aabhassenapati/temperature-display-logger/Images/IMG20250813173202.jpg

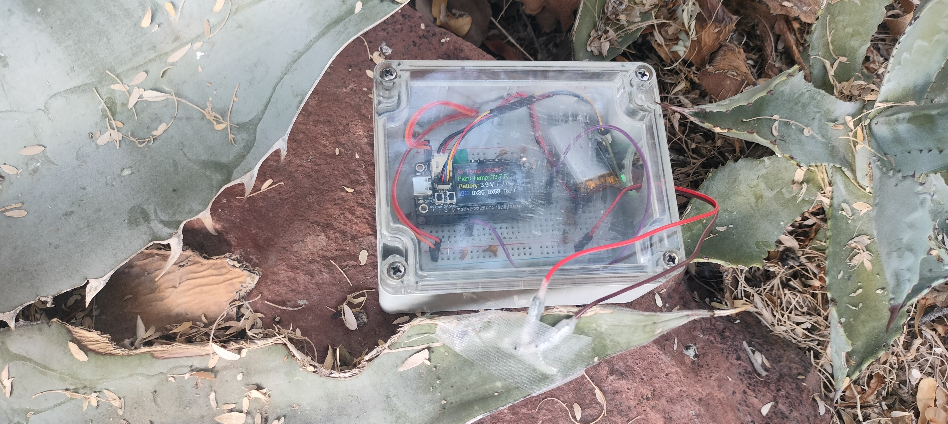
Images/IMG20250813173202.jpg
