aabhassenapati/temperature-display-logger/Images/IMG20250815162052.jpg

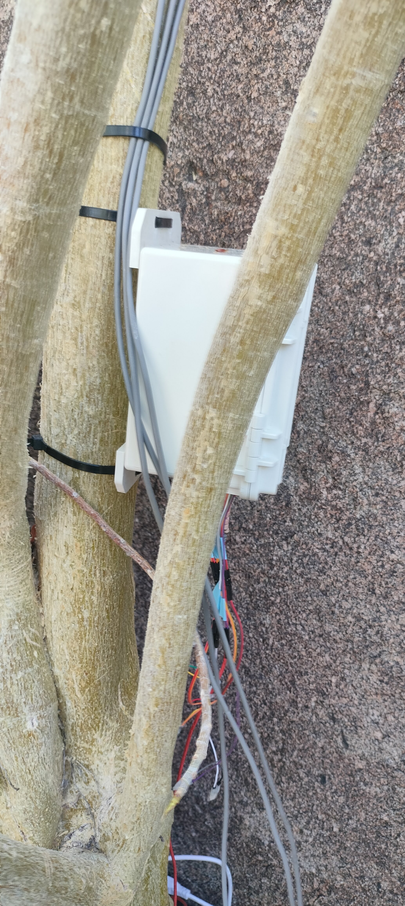
Images/IMG20250815162052.jpg
