aabhassenapati/temperature-display-logger/Images/IMG20250815171557.jpg

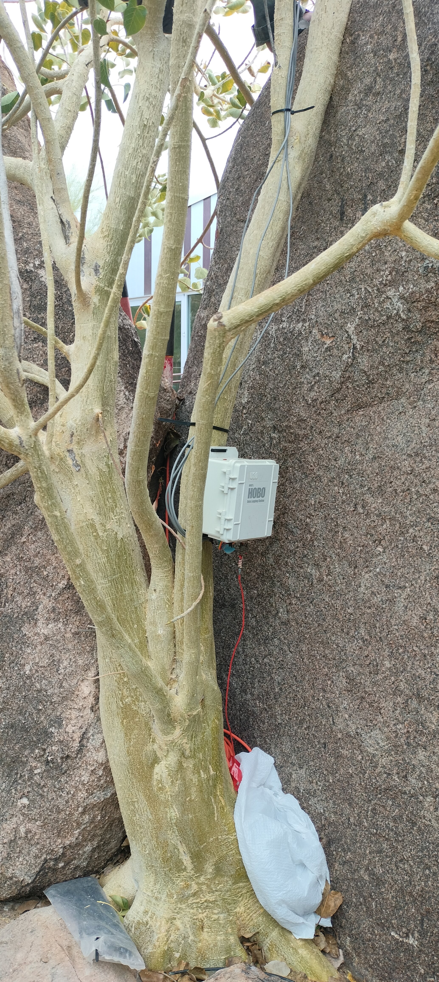
Images/IMG20250815171557.jpg
