aabhassenapati/temperature-display-logger/Images/IMG20250815172234.jpg

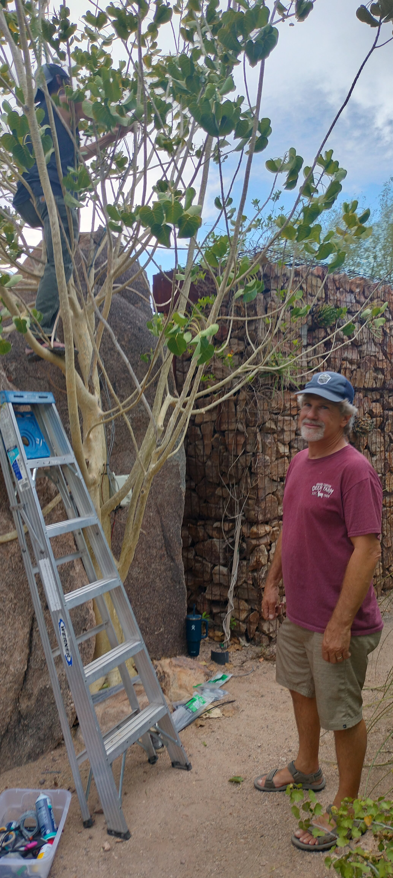
Images/IMG20250815172234.jpg
