aabhassenapati/temperature-display-logger/Images/IMG20250818174235.jpg

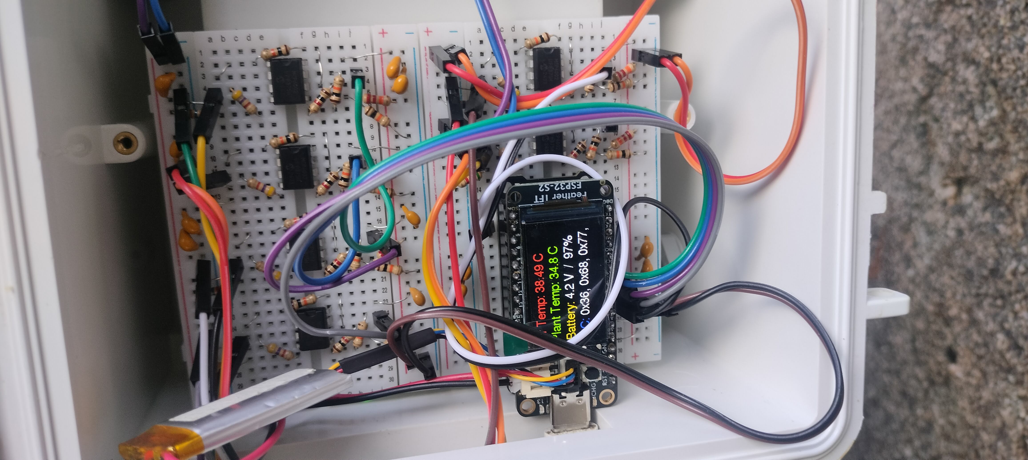
Images/IMG20250818174235.jpg
