aabhassenapati/temperature-display-logger/Images/IMG20250819190731.jpg

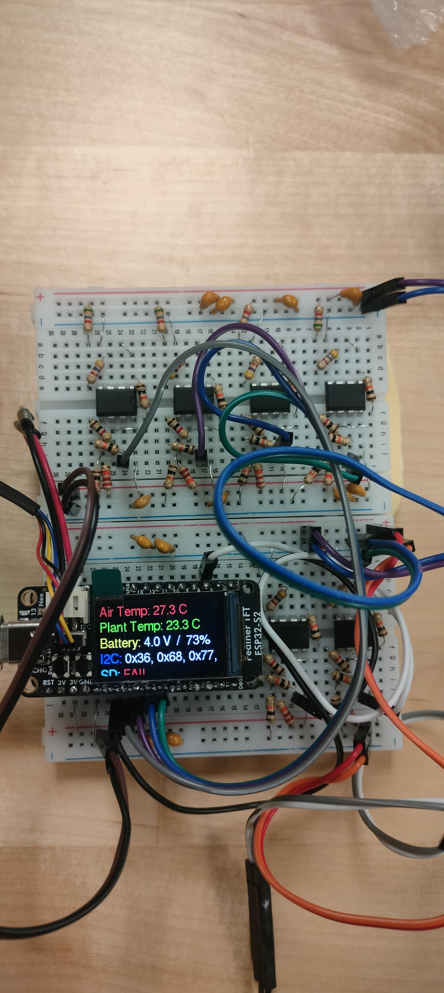
Images/IMG20250819190731.jpg
