aabhassenapati/temperature-display-logger/Images/IMG_2165.jpg

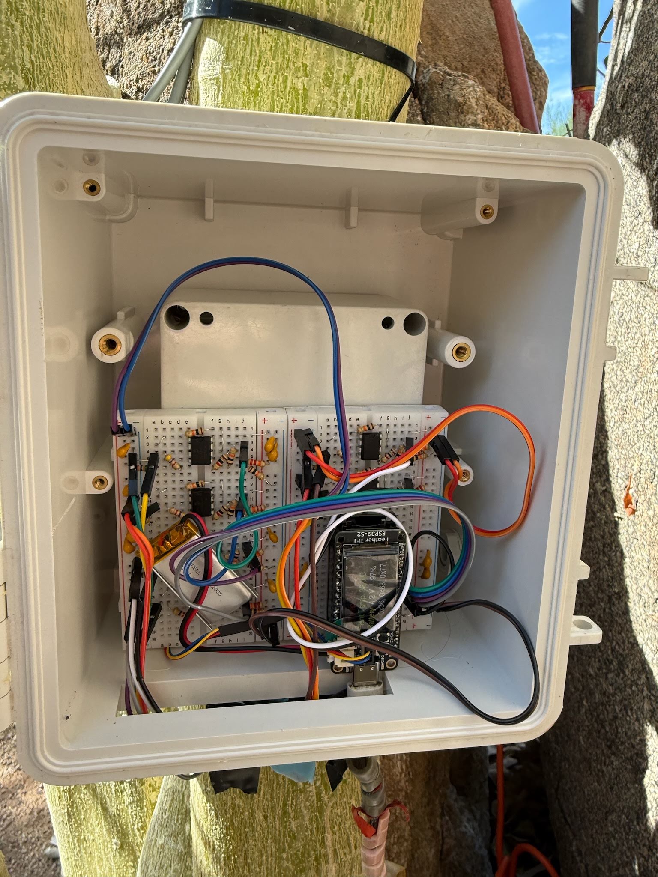
Images/IMG_2165.jpg
