aabhassenapati/temperature-display-logger/Images/IMG_20250822_151914 (4).png

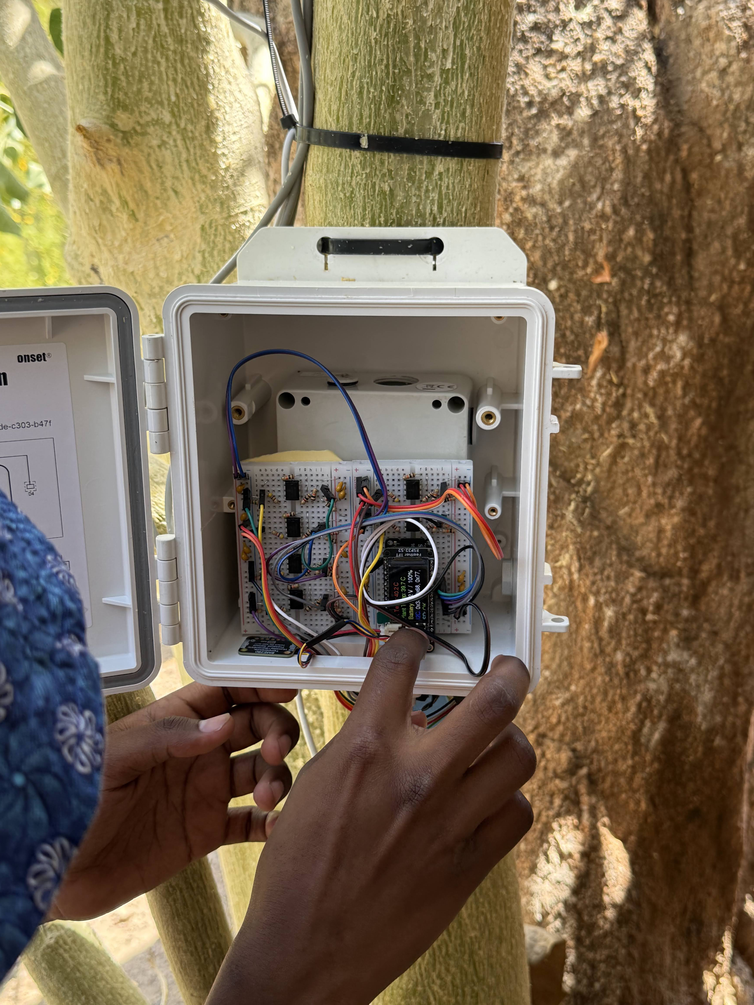
Images/IMG_20250822_151914 (4).png
