aabhassenapati/temperature-display-logger/Images/Screenshot 2025-08-20 at 4.04.33 PM.png

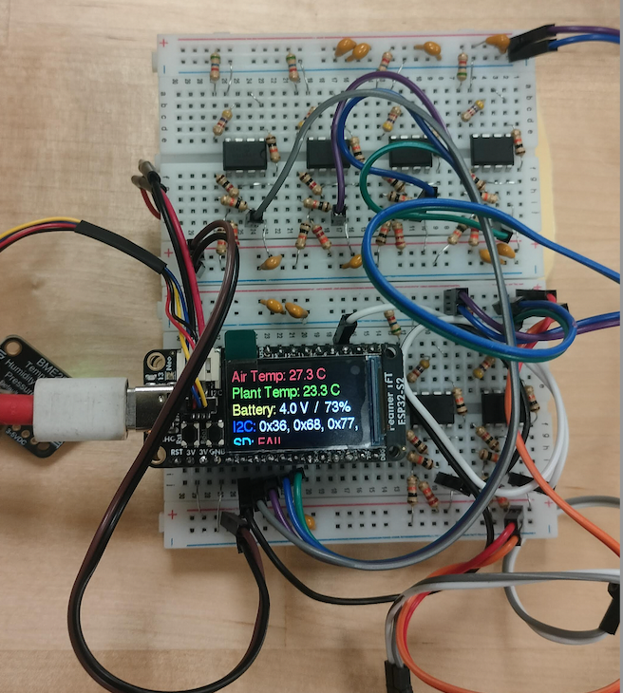
Images/Screenshot 2025-08-20 at 4.04.33 PM.png
