aabhassenapati/temperature-display-logger/Plots/Air Temperature (C) and Relative Humidity (%).png

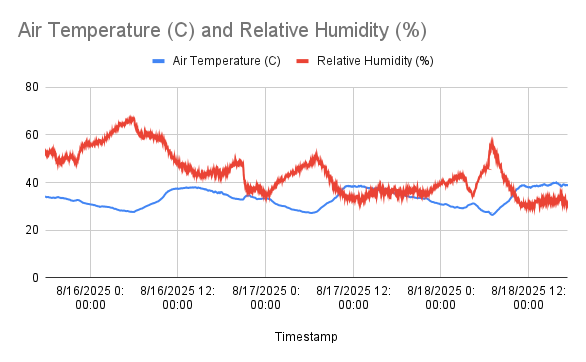
Plots/Air Temperature (C) and Relative Humidity (%).png
