aabhassenapati/temperature-display-logger/Plots/Air Temperature (C) vs Time.png

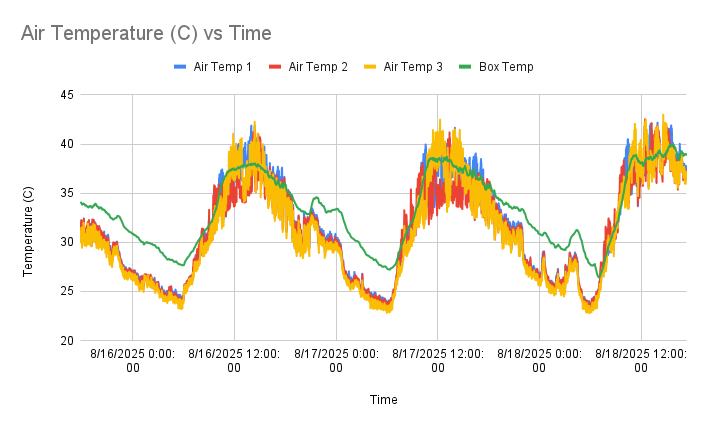
Plots/Air Temperature (C) vs Time.png
