aabhassenapati/temperature-display-logger/Plots/Battery Voltage (V) vs. Timestamp.png

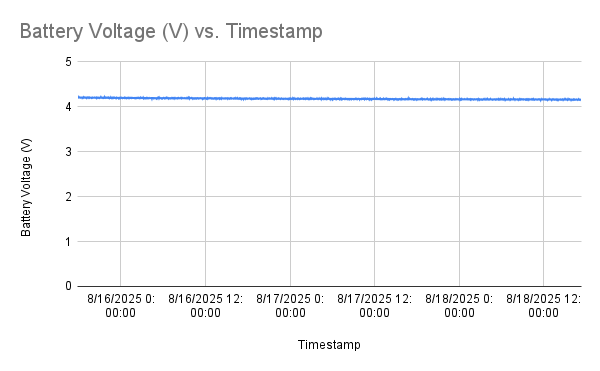
Plots/Battery Voltage (V) vs. Timestamp.png
