aabhassenapati/temperature-display-logger/Plots/Leaf Temperature (C) vs Time.png

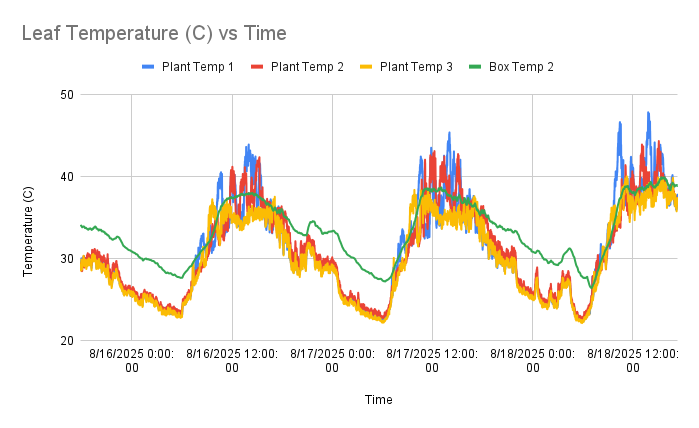
Plots/Leaf Temperature (C) vs Time.png
