aabhassenapati/temperature-display-logger/Plots/Plant 1 Temperature (C) vs Air Temperature (C).png

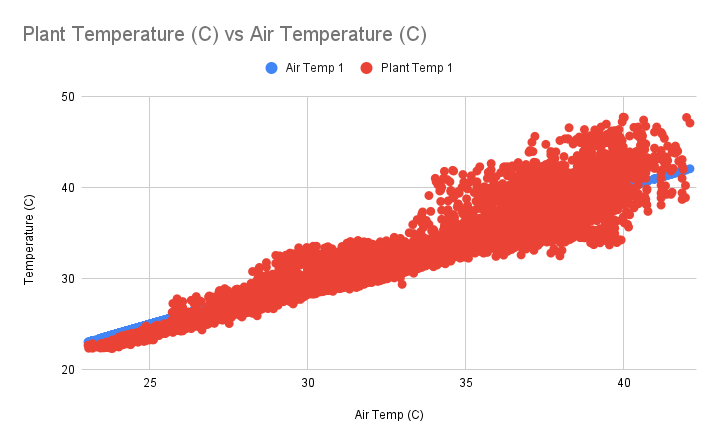
Plots/Plant 1 Temperature (C) vs Air Temperature (C).png
