aabhassenapati/temperature-display-logger/Plots/Plant 2 Temperature (C) vs Air Temperature (C).png

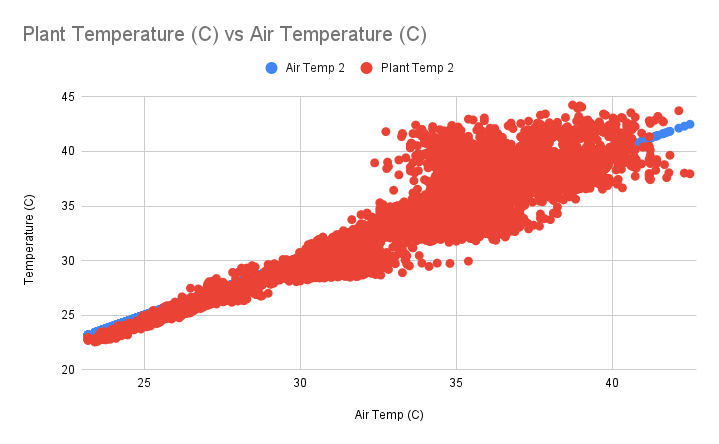
Plots/Plant 2 Temperature (C) vs Air Temperature (C).png
