aabhassenapati/temperature-display-logger/Plots/Temperature (C) vs Time (1).png

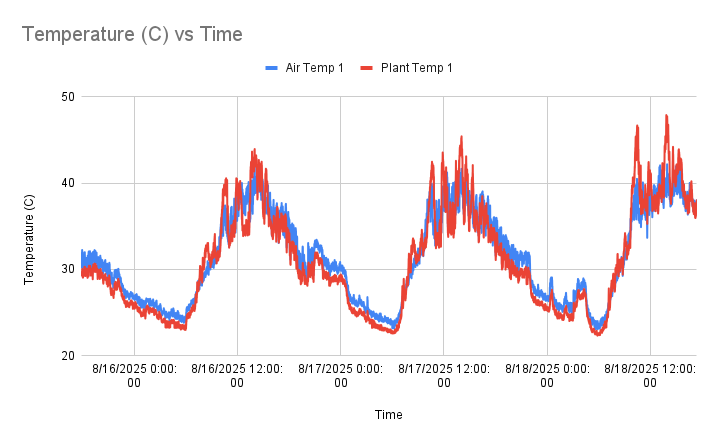
Plots/Temperature (C) vs Time (1).png
