aabhassenapati/temperature-display-logger/Plots/Temperature (C) vs Time (3).png

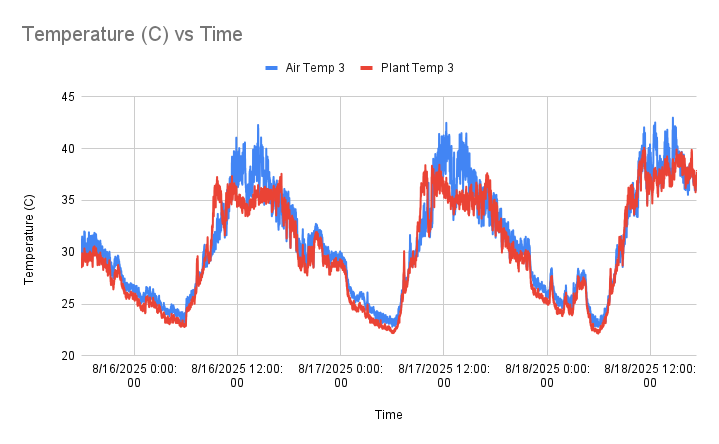
Plots/Temperature (C) vs Time (3).png
