aabhassenapati/temperature-display-logger/Plots/Temperature (C) vs Time.png

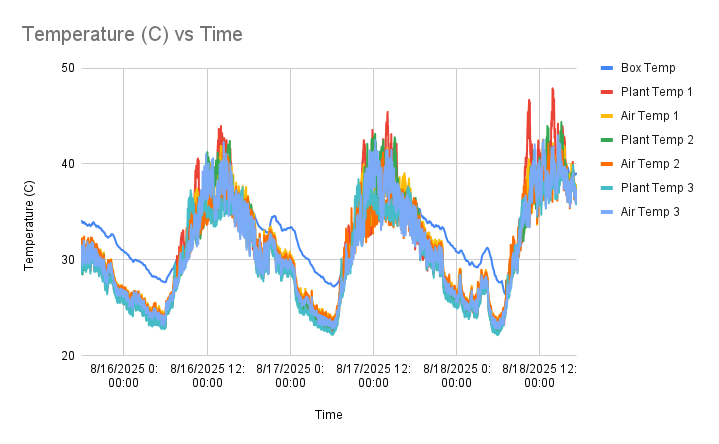
Plots/Temperature (C) vs Time.png
