aabhassenapati/temperature-display-logger/Images/IMG_20250822_151913 (1) (2).png

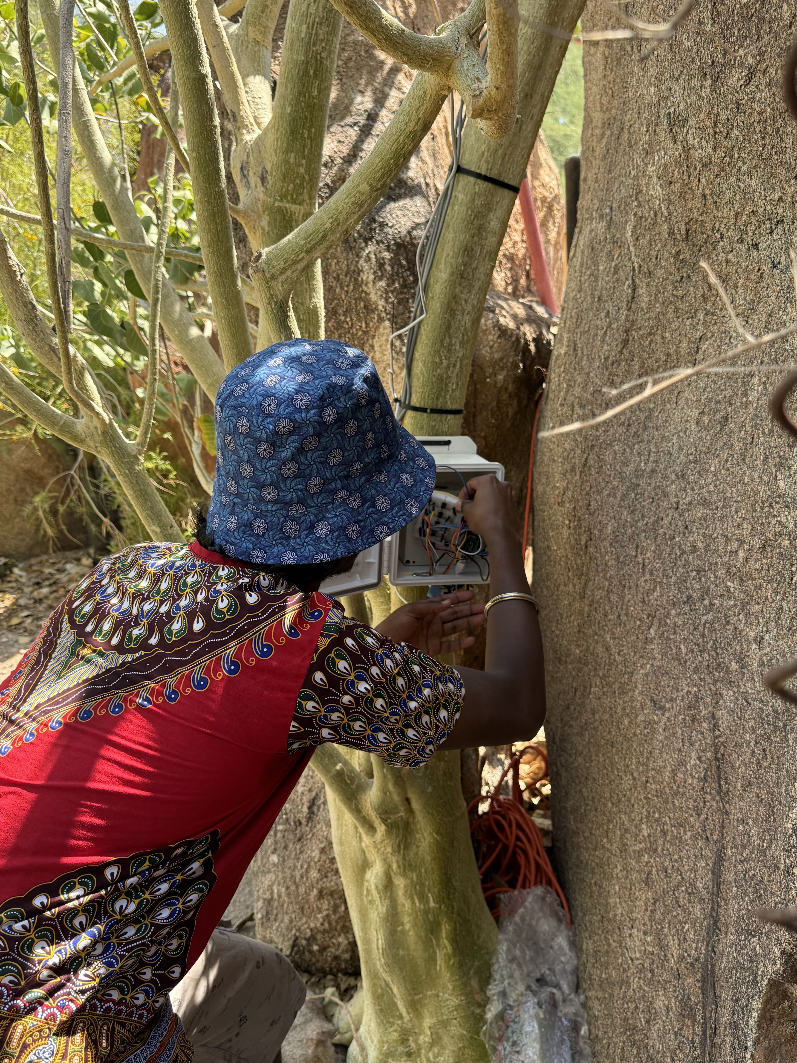
Images/IMG_20250822_151913 (1) (2).png
