aabhassenapati/temperature-display-logger/Images/IMG_20250822_151913 (3).png

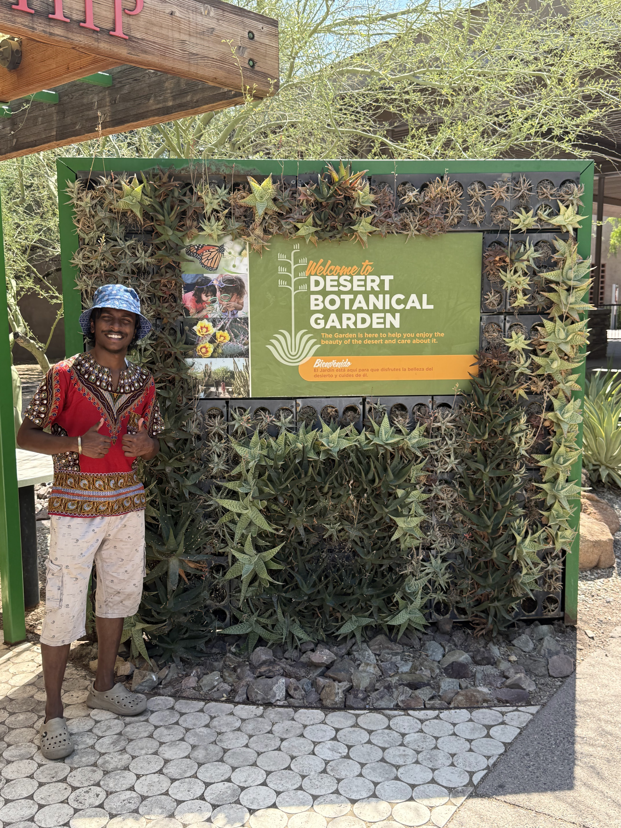
Images/IMG_20250822_151913 (3).png
