aabhassenapati/temperature-display-logger/Images/IMG_20250822_151914.jpg

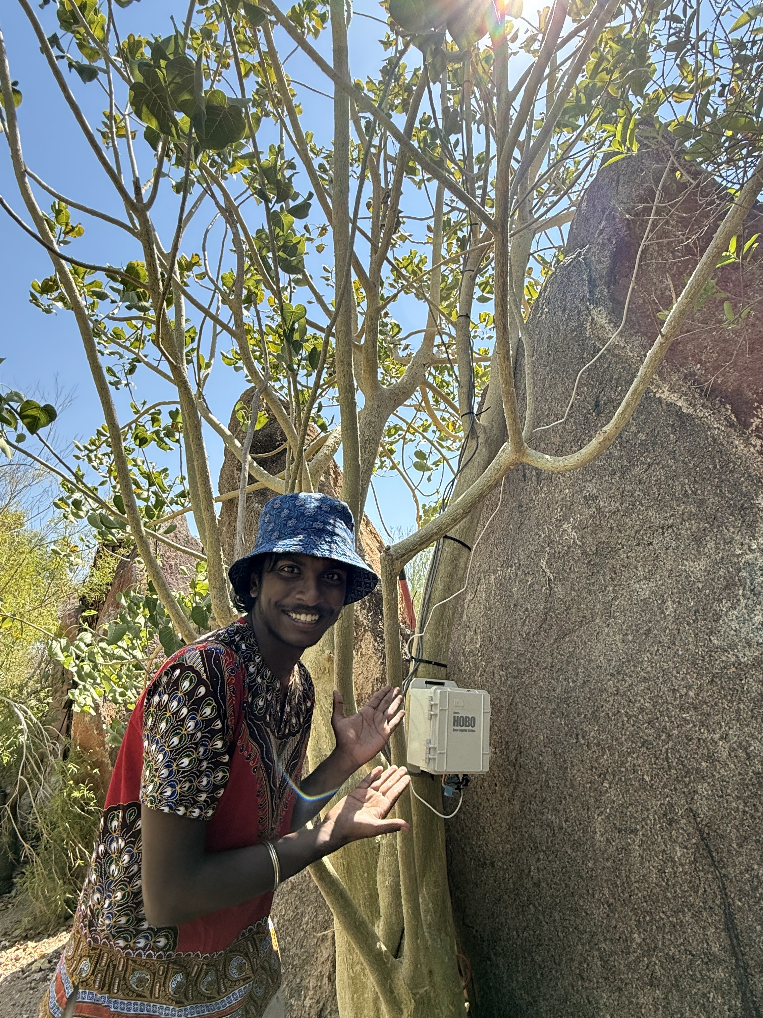
Images/IMG_20250822_151914.jpg
